ZonatedCord/Yggdrasill/PCB/BaseChipOnly_rev2/Esportazione-2026-09-30/preview-3d-top.png

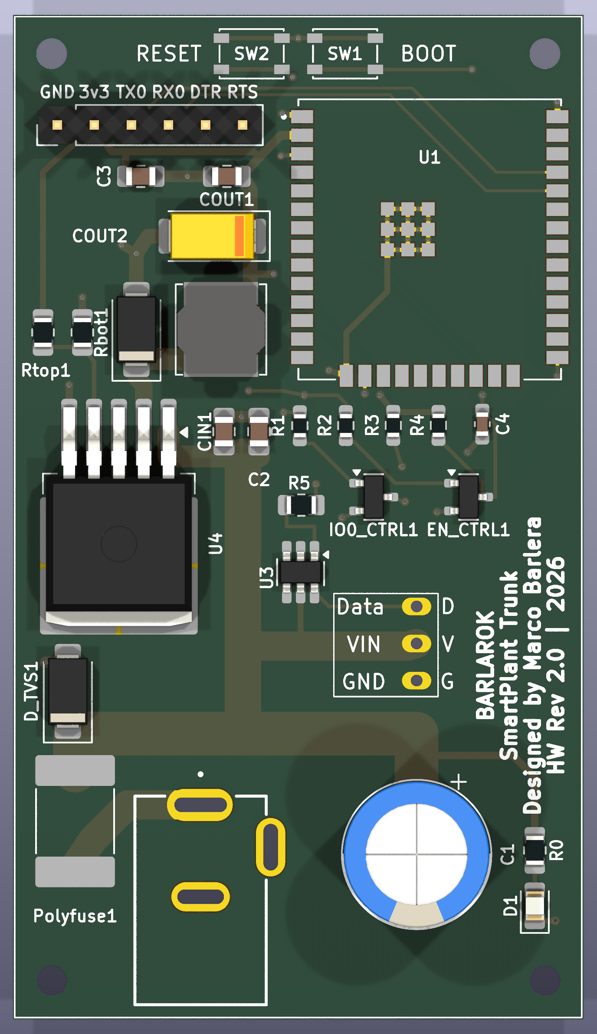
PCB/BaseChipOnly_rev2/Esportazione-2026-09-30/preview-3d-top.png
