ZonatedCord/Yggdrasill/PCB/BaseChipOnly_rev2/simulazioni/grafici/01_autoreset.png

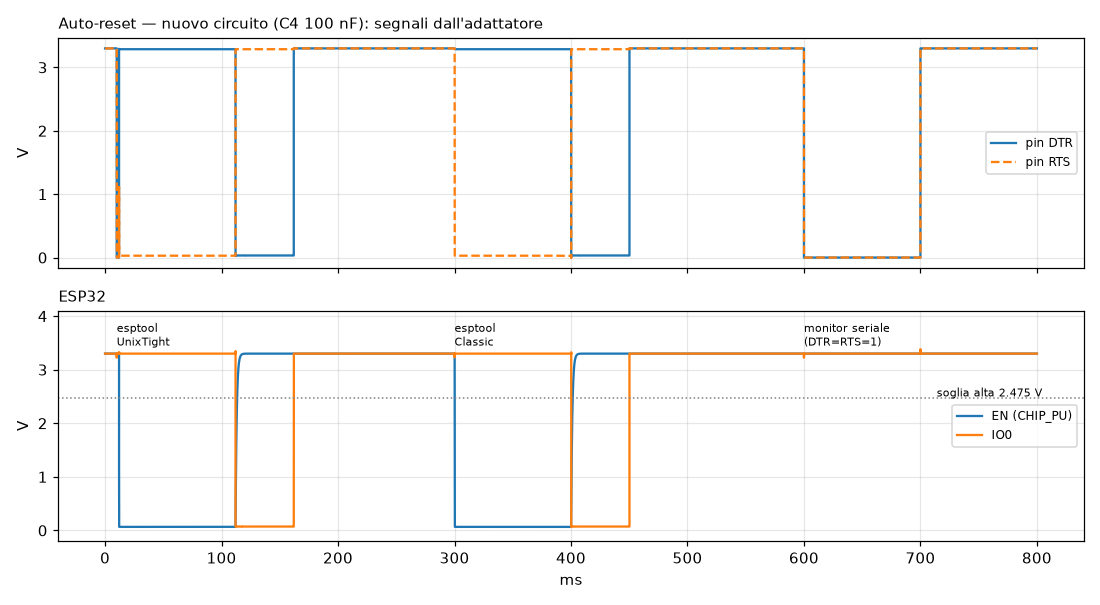
PCB/BaseChipOnly_rev2/simulazioni/grafici/01_autoreset.png
