ZonatedCord/Yggdrasill/PCB/BaseChipOnly_rev2/simulazioni/grafici/01b_autoreset_rev103.png

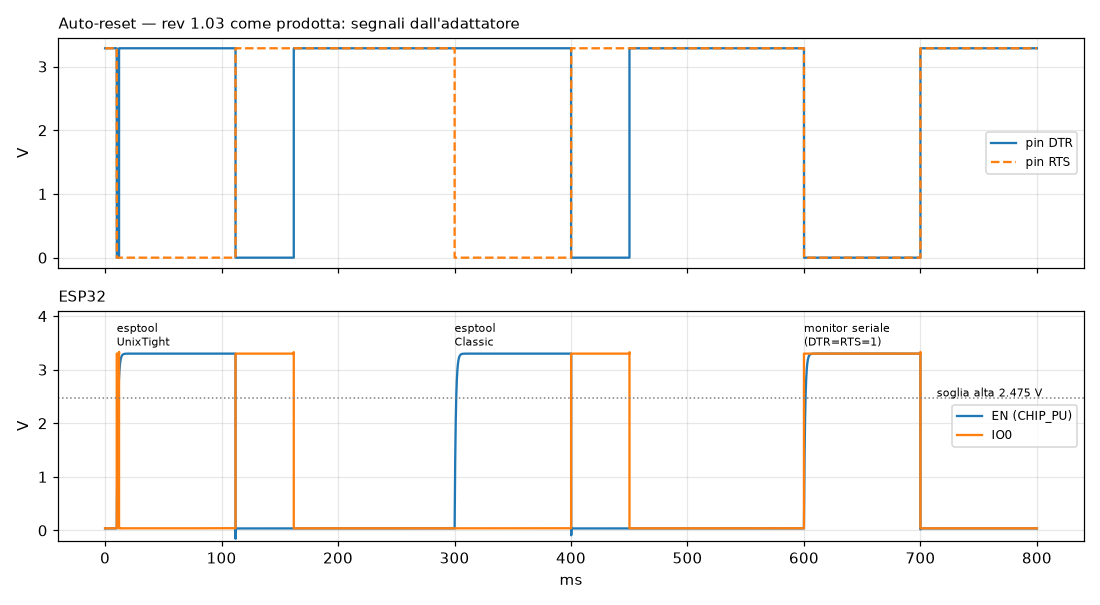
PCB/BaseChipOnly_rev2/simulazioni/grafici/01b_autoreset_rev103.png
