ZonatedCord/Yggdrasill/PCB/BaseChipOnly_rev2/simulazioni/grafici/01c_autoreset_C4_1u.png

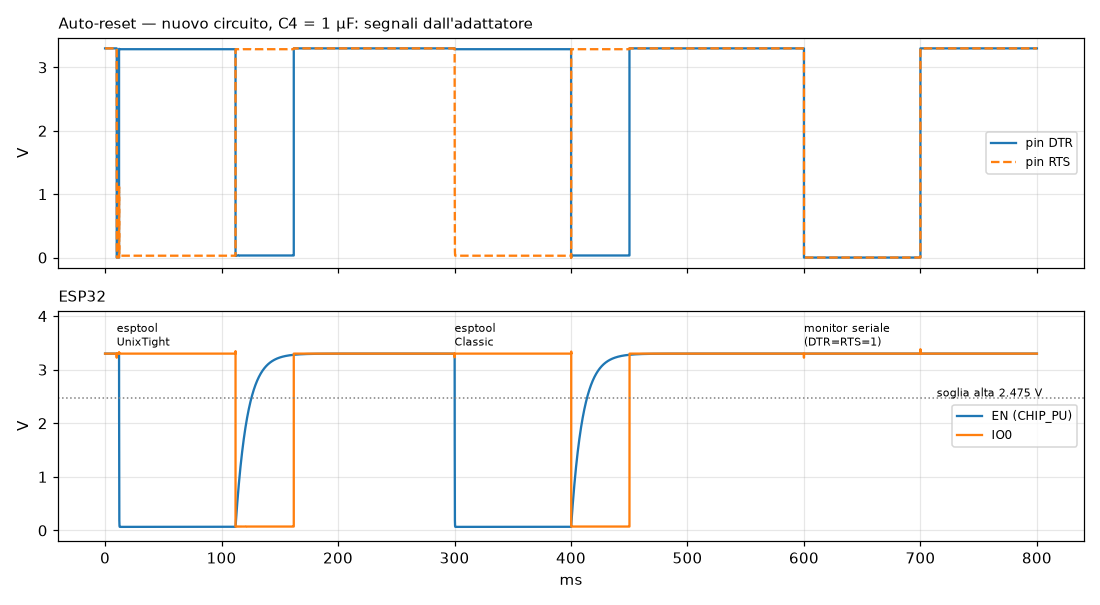
PCB/BaseChipOnly_rev2/simulazioni/grafici/01c_autoreset_C4_1u.png
