ZonatedCord/Yggdrasill/PCB/BaseChipOnly_rev2/simulazioni/grafici/02b_buck_ledload_vsat.png

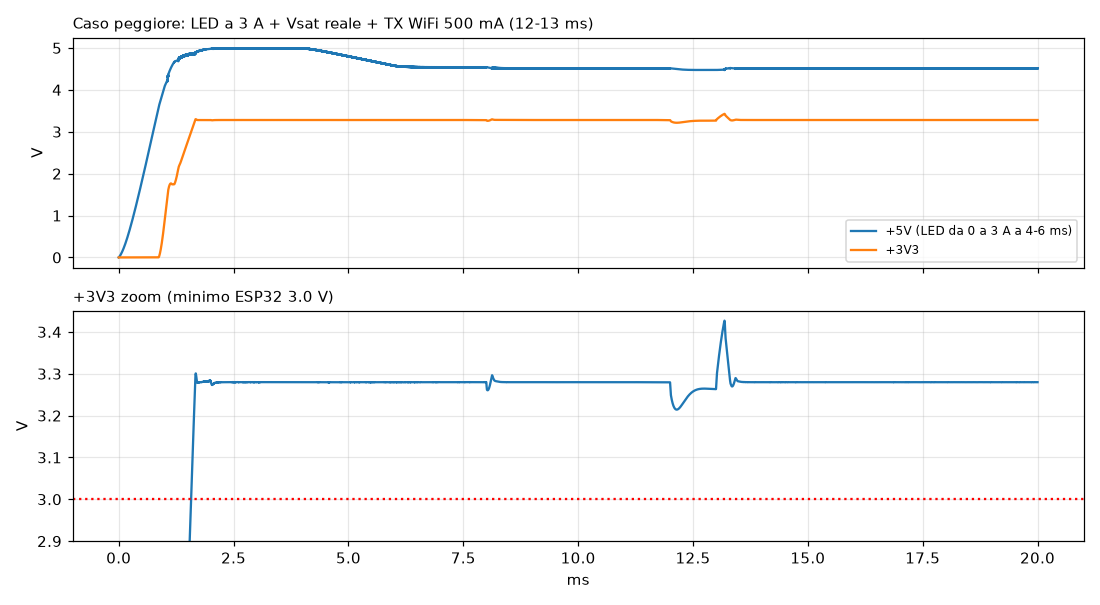
PCB/BaseChipOnly_rev2/simulazioni/grafici/02b_buck_ledload_vsat.png
