ZonatedCord/Yggdrasill/PCB/BaseChipOnly_rev2/simulazioni/grafici/03_poweron.png

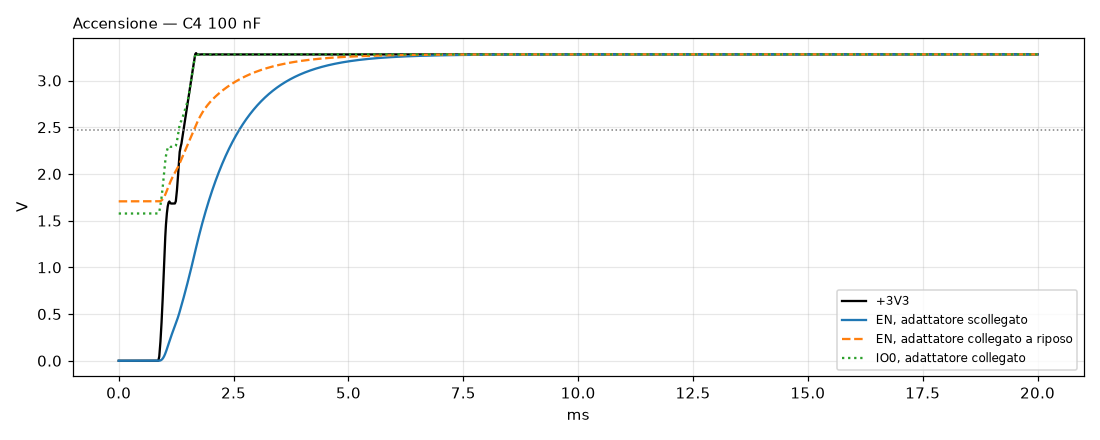
PCB/BaseChipOnly_rev2/simulazioni/grafici/03_poweron.png
