ZonatedCord/Yggdrasill/PCB/BaseChipOnly_rev2/simulazioni/grafici/04_status_led.png

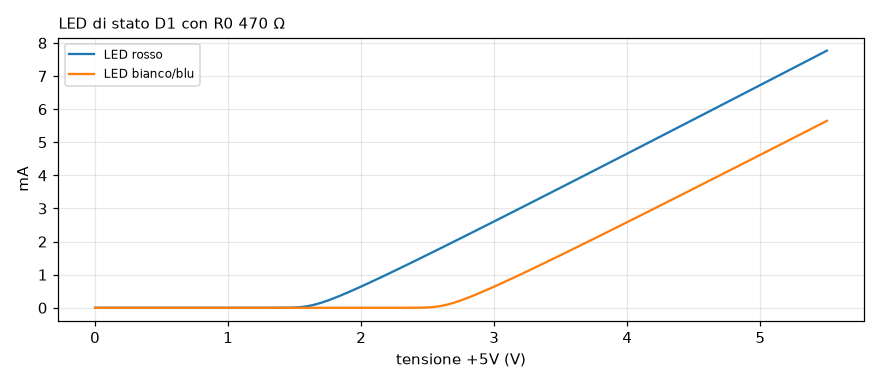
PCB/BaseChipOnly_rev2/simulazioni/grafici/04_status_led.png
