ZonatedCord/Yggdrasill/PCB/BaseChipOnly_rev2/simulazioni/grafici/05_dataline.png

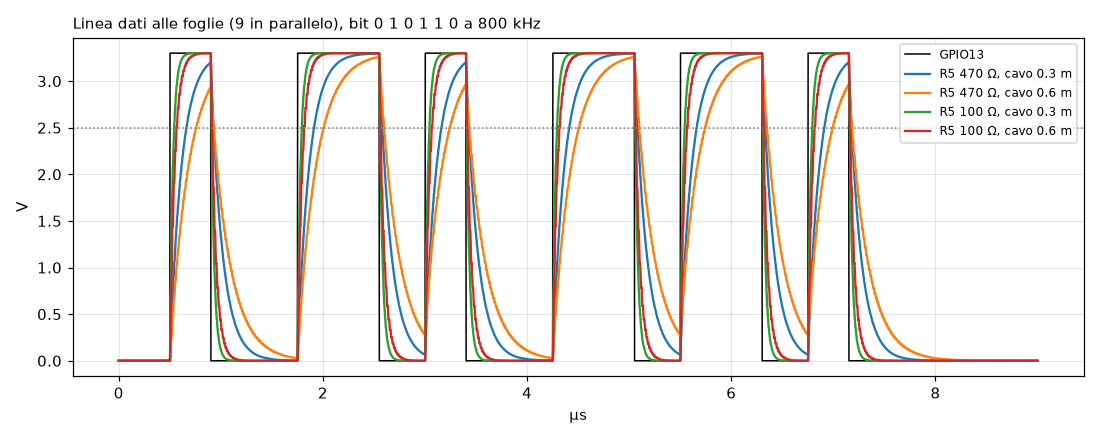
PCB/BaseChipOnly_rev2/simulazioni/grafici/05_dataline.png
